jeffqchen/HORI-DQ-PS2-Controller-Resource/Mini DIN to PS Plug Adapter/PCB/DQ PS2 Controller Adapter.kicad_sch

## KiCad design Mini DIN to PS Plug Adapter/PCB/DQ PS2 Controller Adapter.kicad_sch (2026-02-06)

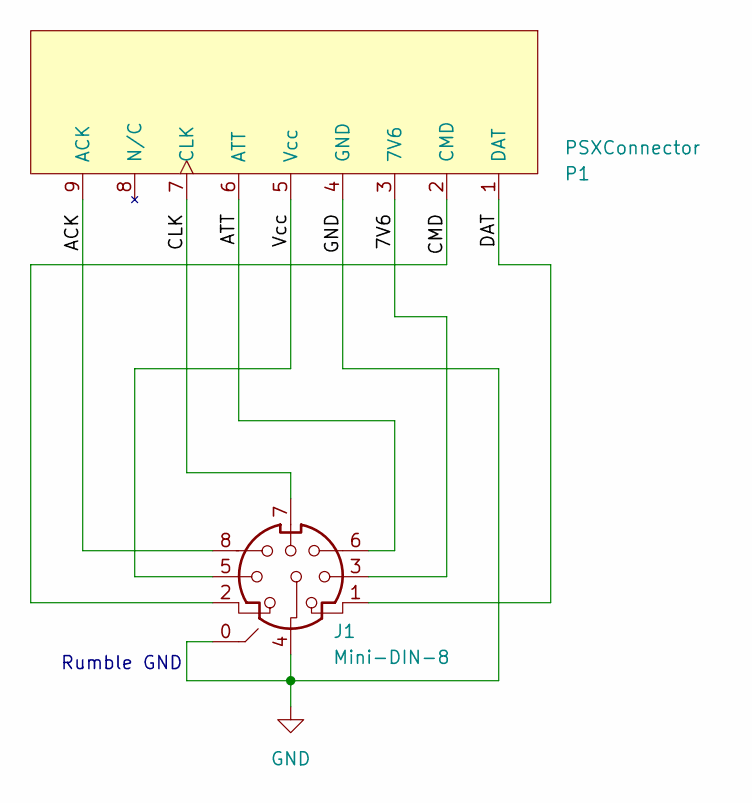
[picture p6: schematic DQ PS2 Controller Adapter.kicad_sch]

Parts:
J1: Mini-DIN-8; Mini DIN 8Pin THT
P1: PSXConnector; PSXController

Connections:
7V6: J1.3, P1.3 (7V6)
ACK: J1.8, P1.9 (ACK)
ATT: J1.6, P1.6 (ATT)
CLK: J1.7, P1.7 (CLK)
CMD: J1.2, P1.2 (CMD)
DAT: J1.1, P1.1 (DAT)
GND: J1.0, J1.4, P1.4 (GND)
Vcc: J1.5, P1.5 (Vcc)

Notes on the sheet:
Rumble GND
